ZyntelliTech/stopwatch-espidf/images/test board diagram.png

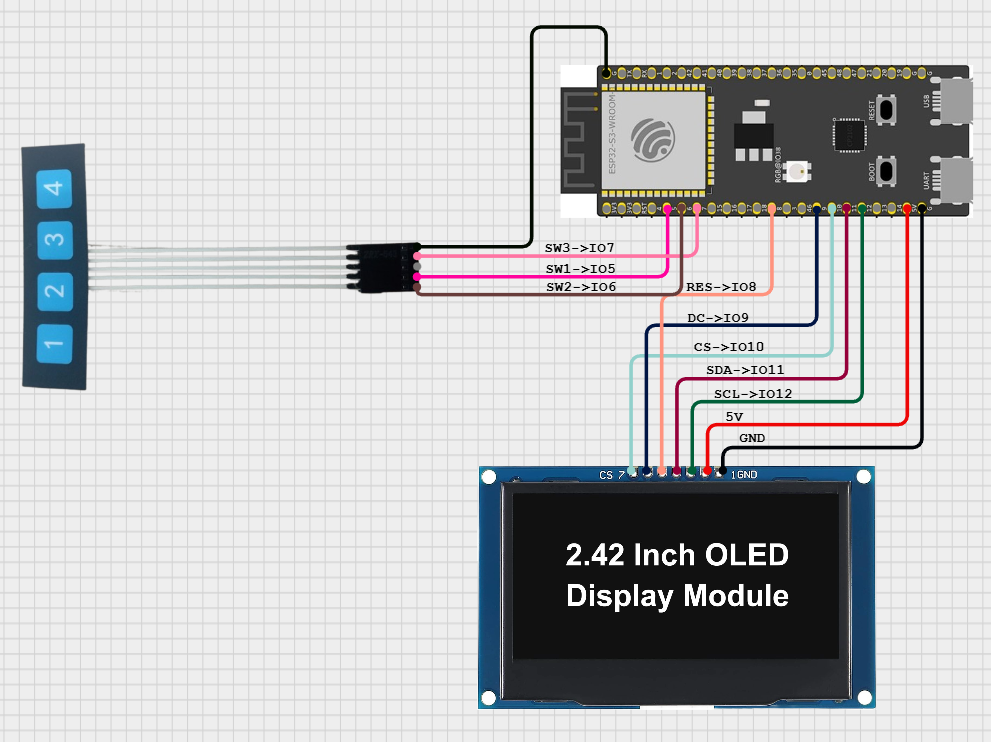
images/test board diagram.png
