ZyntelliTech/stopwatch-espidf/Firmware/main/nvs_storage.c

#include "nvs_storage.h"
#include <string.h>
#include "nvs.h"
#include "nvs_flash.h"
#include "esp_log.h"

static const char *TAG = "NVS_STORAGE";
static const char *NVS_NAMESPACE = "storage";

/* Initialize NVS */
esp_err_t nvs_storage_init(void)
{
    esp_err_t err = nvs_flash_init();

    if (err == ESP_ERR_NVS_NO_FREE_PAGES ||
        err == ESP_ERR_NVS_NEW_VERSION_FOUND) {

        ESP_LOGW(TAG, "Erasing NVS flash");
        ESP_ERROR_CHECK(nvs_flash_erase());
        err = nvs_flash_init();
    }

    if (err == ESP_OK) {
        ESP_LOGI(TAG, "NVS initialized");
    }

    return err;
}

/* Write string */
esp_err_t nvs_write_string(const char *key, const char *value)
{
    if (!key || !value) return ESP_ERR_INVALID_ARG;

    nvs_handle_t handle;
    esp_err_t err = nvs_open(NVS_NAMESPACE, NVS_READWRITE, &handle);
    if (err != ESP_OK) return err;

    err = nvs_set_str(handle, key, value);
    if (err == ESP_OK) {
        err = nvs_commit(handle);
    }

    nvs_close(handle);
    return err;
}

/* Read string */
esp_err_t nvs_read_string(const char *key, char *out, size_t max_len)
{
    if (!key || !out || max_len == 0) return ESP_ERR_INVALID_ARG;

    nvs_handle_t handle;
    size_t required_len = max_len;

    esp_err_t err = nvs_open(NVS_NAMESPACE, NVS_READONLY, &handle);
    if (err != ESP_OK) return err;

    err = nvs_get_str(handle, key, out, &required_len);
    nvs_close(handle);

    return err;
}

/* Erase one key */
esp_err_t nvs_storage_erase_key(const char *key)
{
    if (!key) return ESP_ERR_INVALID_ARG;

    nvs_handle_t handle;
    esp_err_t err = nvs_open(NVS_NAMESPACE, NVS_READWRITE, &handle);
    if (err != ESP_OK) return err;

    err = nvs_erase_key(handle, key);
    if (err == ESP_OK) {
        err = nvs_commit(handle);
    }

    nvs_close(handle);
    return err;
}

/* Erase all keys in namespace */
esp_err_t nvs_storage_erase_all(void)
{
    nvs_handle_t handle;
    esp_err_t err = nvs_open(NVS_NAMESPACE, NVS_READWRITE, &handle);
    if (err != ESP_OK) return err;

    err = nvs_erase_all(handle);
    if (err == ESP_OK) {
        err = nvs_commit(handle);
    }

    nvs_close(handle);
    return err;
}
